sydundar/BenchVolt-PD/Firmware/USB_Power_Source/Core/Src/soft_i2c_3.c

#include <soft_i2c_3.h>

#define true 1
#define false 0

#define I2C3_GPIO_Port GPIOC

/*
#define I2C3_CLEAR_SDA HAL_GPIO_WritePin(I2C3_GPIO_Port, SDA3_Pin, GPIO_PIN_RESET)
#define I2C3_SET_SDA HAL_GPIO_WritePin(I2C3_GPIO_Port, SDA3_Pin, GPIO_PIN_SET)
#define I2C3_CLEAR_SCL HAL_GPIO_WritePin(I2C3_GPIO_Port, SCL3_Pin, GPIO_PIN_RESET)
#define I2C3_SET_SCL HAL_GPIO_WritePin(I2C3_GPIO_Port, SCL3_Pin, GPIO_PIN_SET)
*/
#define I2C3_SET_SDA        (I2C3_GPIO_Port->BSRR = (uint32_t)SDA3_Pin)
#define I2C3_CLEAR_SDA      (I2C3_GPIO_Port->BSRR = (uint32_t)SDA3_Pin << 16U)

#define I2C3_SET_SCL        (I2C3_GPIO_Port->BSRR = (uint32_t)SCL3_Pin)
#define I2C3_CLEAR_SCL      (I2C3_GPIO_Port->BSRR = (uint32_t)SCL3_Pin << 16U)


#define I2C3_DELAY delay3_us(1)

#define MCP4725_ADDR 0x60<<1
#define VHIGH_ADDRS	0x75<<1


bool set_dacVLow(uint16_t reg_data)
{
    reg_data &= 0x0FFF;
    uint8_t data[2];
    data[0] = (reg_data >> 8) & 0x0F;
    data[0] |= 0x00;

    data[1] = reg_data & 0xFF;

     return I2C3_transmit(MCP4725_ADDR, data, 2);
}




void delay3_us(uint32_t us) {
    uint32_t startTick = SysTick->VAL;
    uint32_t ticks = us * (SystemCoreClock / 1000000);
    while ((startTick - SysTick->VAL) < ticks);
}

void I2C3_init(void)
{
    I2C3_SET_SDA;
    I2C3_SET_SCL;
}

void I2C3_start_cond(void)
{
    I2C3_SET_SCL;
    I2C3_SET_SDA;
    I2C3_DELAY;
    I2C3_CLEAR_SDA;
    I2C3_DELAY;
    I2C3_CLEAR_SCL;
    I2C3_DELAY;
}

void I2C3_stop_cond(void)
{
    I2C3_CLEAR_SDA;
    I2C3_DELAY;
    I2C3_SET_SCL;
    I2C3_DELAY;
    I2C3_SET_SDA;
    I2C3_DELAY;
}

void I2C3_write_bit(uint8_t b)
{
    if (b > 0)
        I2C3_SET_SDA;
    else
        I2C3_CLEAR_SDA;

    I2C3_DELAY;
    I2C3_SET_SCL;
    I2C3_DELAY;
    I2C3_CLEAR_SCL;
}

uint8_t I2C3_read_SDA(void)
{
    if (HAL_GPIO_ReadPin(I2C3_GPIO_Port, SDA3_Pin) == GPIO_PIN_SET)
        return 1;
    else
        return 0;
    return 0;
}

// Reading a bit in I2C3:
uint8_t I2C3_read_bit(void)
{
    uint8_t b;

    I2C3_SET_SDA;
    I2C3_DELAY;
    I2C3_SET_SCL;
    I2C3_DELAY;

    b = I2C3_read_SDA();

    I2C3_CLEAR_SCL;

    return b;
}

_Bool I2C3_write_byte(uint8_t B,
                     _Bool start,
                     _Bool stop)
{
    uint8_t ack = 0;

    if (start)
        I2C3_start_cond();

    uint8_t i;
    for (i = 0; i < 8; i++)
    {
        I2C3_write_bit(B & 0x80); // write the most-significant bit
        B <<= 1;
    }

    ack = I2C3_read_bit();

    if (stop)
        I2C3_stop_cond();

    return !ack; //0-ack, 1-nack
}

// Reading a byte with I2C3:
uint8_t I2C3_read_byte(_Bool ack, _Bool stop)
{
    uint8_t B = 0;

    uint8_t i;
    for (i = 0; i < 8; i++)
    {
        B <<= 1;
        B |= I2C3_read_bit();
    }

    if (ack)
        I2C3_write_bit(0);
    else
        I2C3_write_bit(1);

    if (stop)
        I2C3_stop_cond();

    return B;
}

// Sending a byte with I2C3:
_Bool I2C3_send_byte(uint8_t address,
                    uint8_t data)
{
    //    if( I2C3_write_byte( address << 1, true, false ) )   // start, send address, write
    if (I2C3_write_byte(address, true, false)) // start, send address, write
    {
        // send data, stop
        if (I2C3_write_byte(data, false, true))
            return true;
    }

    I2C3_stop_cond(); // make sure to impose a stop if NAK'd
    return false;
}



// Sending a byte of data with I2C3:
_Bool I2C3_send_byte_data(uint8_t address,
                         uint8_t reg,
                         uint8_t data)
{
    if (I2C3_write_byte(address, true, false))
    {
        if (I2C3_write_byte(reg, false, false)) // send desired register
        {
            if (I2C3_write_byte(data, false, true))
                return true; // send data, stop
        }
    }

    I2C3_stop_cond();
    return false;
}

// Receiving a byte of data with I2C3:
uint8_t I2C3_receive_byte_data(uint8_t address,
                              uint8_t reg)
{

    if (I2C3_write_byte(address, true, false))
    {
        if (I2C3_write_byte(reg, false, false)) // send desired register
        {
            if (I2C3_write_byte((address) | 0x01, true, false)) // start again, send address, read
            {
                return I2C3_read_byte(false, true); // read data
            }
        }
    }

    I2C3_stop_cond();
    return 0; // return zero if NACKed
}




_Bool I2C3_transmit(uint8_t address, uint8_t data[], uint8_t size)
{
    if (I2C3_write_byte(address, true, false)) // first byte
    {
        for (int i = 0; i < size; i++)
        {
            if (i == size - 1)
            {
                if (I2C3_write_byte(data[i], false, true))
                    return true;
            }
            else
            {
                if (!I2C3_write_byte(data[i], false, false))
                    break; //last byte
            }
        }
    }

    I2C3_stop_cond();
    return false;
}

_Bool I2C3_receive(uint8_t address, uint8_t reg[], uint8_t *data, uint8_t reg_size, uint8_t size)
{
    if (I2C3_write_byte(address, true, false))
    {
        for (int i = 0; i < reg_size; i++)
        {
            if (!I2C3_write_byte(reg[i], false, false))
                break;
        }
        if (I2C3_write_byte(address | 0x01, true, false)) // start again, send address, read
        {
            for (int j = 0; j < size; j++)
            {
                _Bool ack = (j < size - 1);
                _Bool stop = (j == size - 1);
                *data++ = I2C3_read_byte(ack, stop);
            }
            return true;
        }
    }
    I2C3_stop_cond();
    return false;
}


//////////////////////////////////////////////////////////////////////////
//////////////////////////////////////////////////////////////////////////
//////////////////////////////////////////////////////////////////////////


void VAdjHigh_InitInternalFeedback() {
	uint8_t status1 = I2C3_receive_byte_data(VHIGH_ADDRS, REG_STATUS);
	uint8_t status2 = I2C3_receive_byte_data(VHIGH_ADDRS, REG_STATUS);

    uint8_t vfs = I2C3_receive_byte_data(VHIGH_ADDRS, REG_VOUT_FS);
    if (vfs == 0xFF) return;
    vfs &= ~(0x80 | 0x03);
    vfs |= 0x03;
    I2C3_send_byte_data(VHIGH_ADDRS, REG_VOUT_FS, vfs);
}

void VAdjHigh_EnableOutput(bool en) {
    uint8_t mode = I2C3_receive_byte_data(VHIGH_ADDRS, REG_MODE);
    if (en) mode |= 0x80;
    else mode &= ~0x80;
    I2C3_send_byte_data(VHIGH_ADDRS, REG_MODE, mode);
}

void VAdjHigh_SetVoltage(float voltage) {
    if (voltage < TPS_VOUT_MIN_V) voltage = TPS_VOUT_MIN_V;
    if (voltage > TPS_VOUT_MAX_V) voltage = TPS_VOUT_MAX_V;

    float vrefV = voltage * TPS_FB_RATIO_VAL;
    float codeF = (vrefV - TPS_VREF_OFFSET_V) / TPS_VREF_LSB_V;

    if (codeF < 0.0f) codeF = 0.0f;
    if (codeF > TPS_VREF_MAXCODE) codeF = (float)TPS_VREF_MAXCODE;

    uint16_t code = (uint16_t)(codeF + 0.5f);
    I2C3_send_byte_data(VHIGH_ADDRS, REG_REF_LSB, (uint8_t)(code & 0xFF));
    I2C3_send_byte_data(VHIGH_ADDRS, REG_REF_MSB, (uint8_t)((code >> 8) & 0x07));
}

void VAdjHigh_SetCurrentLimit(float current) {
    if (current <= 0.0f) {
        I2C3_send_byte_data(VHIGH_ADDRS, REG_IOUT_LIMIT, 0x00);
        return;
    }
    float vsenseV = current * TPS_RSENSE_OHM;
    float codeF = vsenseV / TPS_ISENSE_LSB_V;
    if (codeF > 127.0f) codeF = 127.0f;

    uint8_t code = (uint8_t)(codeF + 0.5f);
    I2C3_send_byte_data(VHIGH_ADDRS, REG_IOUT_LIMIT, (0x80 | (code & 0x7F)));
}

uint8_t VAdjHigh_GetStatus() {
    return I2C3_receive_byte_data(VHIGH_ADDRS, REG_STATUS);
}

/////////////////////
void InitVAdjHigh() { VAdjHigh_InitInternalFeedback(); }
void EnVAdjHighOutput(bool onoff) { VAdjHigh_EnableOutput(onoff); }
void SetVoltageVAdjHigh(float voltage){ VAdjHigh_SetVoltage(voltage); }
void SetVAdjHighCurrentLimit(float current) { VAdjHigh_SetCurrentLimit(current); }
