sydundar/BenchVolt-PD/Firmware/USB_Power_Source/Core/Inc/stm32_sw_i2c.h

/*
  stm32_sw_i2c.h - Library for implementing I2C in SW on any GPIO on STM32 MCU.
  Created by Mawaba Pascal Dao, Dec 2, 2020.
  Released into the public domain.
*/


#include "main.h"


void I2C_init(void);
void I2C_start_cond(void);
void I2C_stop_cond(void);
static inline void I2C_write_bit(uint8_t b) __attribute__((always_inline));
static inline uint8_t I2C_read_bit(void) __attribute__((always_inline));
uint8_t I2C_read_SDA(void);
_Bool I2C_write_byte(uint8_t B, _Bool start, _Bool stop);
uint8_t I2C_read_byte(_Bool ack, _Bool stop);
_Bool I2C_send_byte(uint8_t address, uint8_t data);
uint8_t I2C_receive_byte(uint8_t address);
_Bool I2C_send_byte_data(uint8_t address, uint8_t reg, uint8_t data);
uint8_t I2C_receive_byte_data(uint8_t address, uint8_t reg);
_Bool I2C_transmit(uint8_t address, uint8_t data[], uint8_t size);
_Bool I2C_receive(uint8_t address, uint8_t reg[], uint8_t *data, uint8_t reg_size, uint8_t size);

HAL_StatusTypeDef I2C_Write_USB_PD(uint8_t Port, uint16_t Address, uint8_t *DataW, uint16_t Length);

HAL_StatusTypeDef I2C_Read_USB_PD(uint8_t Port, uint16_t Address ,uint8_t *DataR ,uint16_t Length);
