sydundar/BenchVolt-PD/Firmware/USB_Power_Source/Core/Inc/STUSB_NVM.h

#include "main.h"

uint8_t Sector0[8] = {0x00,0x00,0xB0,0xAA,0x00,0x45,0x00,0x02};
uint8_t Sector1[8] = {0x00,0x40,0x9D,0x1C,0xF0,0x01,0x00,0xDF};
uint8_t Sector2[8] = {0x32,0x40,0x0F,0x01,0x32,0x0A,0xFC,0xF1};
uint8_t Sector3[8] = {0x00,0x19,0x54,0xAA,0x57,0x35,0x5F,0x00};
uint8_t Sector4[8] = {0x00,0x64,0x90,0x21,0x43,0x00,0x50,0xFB};
