sydundar/BenchVolt-PD/Firmware/Bootloader/Core/Src/main.c

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
/* Includes ------------------------------------------------------------------*/
#include "main.h"
#include "usb_device.h"

/* USER CODE BEGIN Includes */
#include <stdio.h>
#include <string.h>
#include "Flash.h"
#include "usbd_cdc_if.h"
#include "st7789.h"

// Flash Addresses
#define BOOTLOADER_FLASH_ADDR       0x08000000
#define PARAM_PAGE_ADDR			    0x0801F800    // Starts after 32KB Bootloader
#define MAIN_APP_FLASH_ADDR         0x08008000    // Starts after 2KB Config Page
#define VECTOR_TABLE_SIZE  0xC0U





// Protocol Commands
#define CMD_START                  0x01
#define CMD_DATA                   0x02
#define CMD_END                    0x03
#define CMD_JUMP_ONLY              0x04
#define CMD_ERASE_CRC              0x05
#define CMD_JUMP_ONLY              0x04
#define CMD_ERASE_CRC              0x05
// Protocol Responses
#define ACK                        0x06
#define NACK                       0x15


/* USER CODE END Includes */

CRC_HandleTypeDef hcrc;

SPI_HandleTypeDef hspi1;
DMA_HandleTypeDef hdma_spi1_tx;

void SystemClock_Config(void);
static void MX_GPIO_Init(void);
static void MX_DMA_Init(void);
static void MX_CRC_Init(void);
static void MX_SPI1_Init(void);
/* USER CODE BEGIN 0 */

char MBCodeBuiltDateTime[30];
uint8_t flashbuffer[128] __attribute__((aligned(4)));

uint8_t usb_rx_buffer[256];
volatile uint32_t usb_rx_len = 0;
volatile uint8_t usb_data_ready = 0;

uint32_t write_address = MAIN_APP_FLASH_ADDR;
uint32_t total_file_size = 0;
uint8_t bootloader_active = 0;

void SystemClock_Config(void);
static void MX_GPIO_Init(void);
static void MX_CRC_Init(void);
void PrintBuildDate(void);
void WriteToDevice(char* commandString);
void JumpToMainApp(void);
uint32_t calculate_crc32(uint8_t *data, uint32_t size);
void ReadFlashBuffer(void);
void WriteCRC(unsigned char *data);
uint32_t ReadCRC(void);
void WriteAppSize(uint32_t size);
uint32_t ReadAppSize(void);
void Bootloader_Protocol_Handler(void);
void Send_USB_Response(uint8_t res);

void PrintBuildDate(void)
{
    snprintf(MBCodeBuiltDateTime, 30, "%s %s", __DATE__, __TIME__);
    WriteToDevice("Code Build Date: ");
    WriteToDevice(MBCodeBuiltDateTime);
    WriteToDevice("\r\n\r\n");
}

void WriteToDevice(char* commandString)
{
    CDC_Transmit_FS((uint8_t*)commandString, strlen(commandString));
}


void JumpToMainApp(void)
{
    uint32_t appStack = *(volatile uint32_t*)MAIN_APP_FLASH_ADDR;
    uint32_t appEntry = *(volatile uint32_t*)(MAIN_APP_FLASH_ADDR + 4);

    if ((appStack < 0x20000000U) || (appStack > 0x20004000U))
        return;

    __disable_irq();

    SysTick->CTRL = 0;
    SysTick->LOAD = 0;
    SysTick->VAL  = 0;

    USB->CNTR = USB_CNTR_FRES;
    USB->CNTR = 0;
    USB->BCDR &= ~USB_BCDR_DPPU;
    __HAL_RCC_USB_CLK_DISABLE();

    for (uint32_t i = 0; i < 8; i++)
    {
        NVIC->ICER[i] = 0xFFFFFFFF;
        NVIC->ICPR[i] = 0xFFFFFFFF;
    }

    for (uint32_t i = 0; i < VECTOR_TABLE_SIZE / 4; i++)
    {
        ((volatile uint32_t*)0x20000000U)[i] =
            ((volatile uint32_t*)MAIN_APP_FLASH_ADDR)[i];
    }

    __HAL_RCC_SYSCFG_CLK_ENABLE();

    SYSCFG->CFGR1 &= ~SYSCFG_CFGR1_MEM_MODE;
    SYSCFG->CFGR1 |= SYSCFG_CFGR1_MEM_MODE_0 | SYSCFG_CFGR1_MEM_MODE_1;

    __DSB();
    __ISB();

    __set_MSP(appStack);

    ((void (*)(void))appEntry)();

    while (1);
}


uint32_t calculate_crc32(uint8_t *data, uint32_t size)
{
    uint32_t crc = 0xFFFFFFFF;
    for (uint32_t i = 0; i < size; i++)
    {
        crc = crc ^ (uint32_t)data[i];
        for (uint32_t j = 0; j < 8; j++)
        {
            if (crc & 0x80000000) crc = (crc << 1) ^ 0x04C11DB7;
            else crc <<= 1;
        }
    }
    return crc;
}

void ReadFlashBuffer(void)
{
    ReadFlash((uint32_t*)PARAM_PAGE_ADDR, (uint32_t*)flashbuffer, 32);
}

void WriteCRC(unsigned char *data)
{
    ReadFlashBuffer();
    flashbuffer[16] = data[0]; flashbuffer[17] = data[1];
    flashbuffer[18] = data[2]; flashbuffer[19] = data[3];
    WriteFlash(PARAM_PAGE_ADDR, (uint32_t*)flashbuffer, sizeof(flashbuffer)/sizeof(uint32_t));
    HAL_Delay(10);
}

void WriteBootParams(uint32_t crc, uint32_t size)
{
    FLASH_EraseInitTypeDef EraseInitStruct;
    uint32_t PageError = 0;

    HAL_FLASH_Unlock();

    // Sadece parametre sayfasını sil (Uygulamaya asla dokunmaz)
    EraseInitStruct.TypeErase = FLASH_TYPEERASE_PAGES;
    EraseInitStruct.PageAddress = PARAM_PAGE_ADDR;
    EraseInitStruct.NbPages = 1;
    HAL_FLASHEx_Erase(&EraseInitStruct, &PageError);

    // CRC ve Boyut bilgilerini mühürle
    HAL_FLASH_Program(FLASH_TYPEPROGRAM_WORD, PARAM_PAGE_ADDR, crc);
    HAL_FLASH_Program(FLASH_TYPEPROGRAM_WORD, PARAM_PAGE_ADDR + 4, size);

    HAL_FLASH_Lock();
}


uint32_t ReadCRC(void)
{
    return *(volatile uint32_t*)PARAM_PAGE_ADDR;
}

uint32_t ReadAppSize(void)
{
    return *(volatile uint32_t*)(PARAM_PAGE_ADDR + 4);
}

void WriteAppSize(uint32_t size)
{
    ReadFlashBuffer();
    flashbuffer[20] = (uint8_t)(size & 0xFF);
    flashbuffer[21] = (uint8_t)((size >> 8) & 0xFF);
    flashbuffer[22] = (uint8_t)((size >> 16) & 0xFF);
    flashbuffer[23] = (uint8_t)((size >> 24) & 0xFF);
    WriteFlash(PARAM_PAGE_ADDR, (uint32_t*)flashbuffer, sizeof(flashbuffer)/sizeof(uint32_t));
    HAL_Delay(10);
}



void Send_USB_Response(uint8_t res)
{
    uint32_t start_tick = HAL_GetTick();
    while (CDC_Transmit_FS(&res, 1) == USBD_BUSY)
    {
        if ((HAL_GetTick() - start_tick) > 100) break;
        HAL_Delay(1);
    }
}

void Bootloader_Protocol_Handler(void)
{
    if (!usb_data_ready) return;
    uint8_t cmd = usb_rx_buffer[0];

    if (cmd == CMD_START)
        {
            total_file_size = usb_rx_buffer[1] | (usb_rx_buffer[2] << 8) | (usb_rx_buffer[3] << 16) | (usb_rx_buffer[4] << 24);
            write_address = MAIN_APP_FLASH_ADDR;
            bootloader_active = 1;

            //Bootloader_ShowProgress(0, total_file_size);
            WriteBootParams(0xFFFFFFFF, 0xFFFFFFFF);  // Delete existing CRC

            if (Flash_EraseAppArea(MAIN_APP_FLASH_ADDR, total_file_size) == 0) Send_USB_Response(ACK);
            else Send_USB_Response(NACK);
        }

    else if (cmd == CMD_DATA && bootloader_active)
        {
            uint16_t len = usb_rx_buffer[1] | (usb_rx_buffer[2] << 8);
            uint8_t *payload = &usb_rx_buffer[3];

            // DİKKAT: Veriyi 4'ün katına (Word Alignment) yuvarlıyoruz!
            uint32_t word_count = (len + 3) / 4;
            uint32_t aligned_buffer[64]; // Maksimum paket boyutunu kaldıracak havuz

            // 1. Buffer'ı 0xFF ile doldur (Boş kalan byte'lar Flash'ta 0xFF olarak kalmalıdır)
            memset(aligned_buffer, 0xFF, sizeof(aligned_buffer));

            // 2. Gelen 8-bitlik raw veriyi güvenli 32-bitlik havuza kopyala
            memcpy(aligned_buffer, payload, len);

            // 3. Özel Flash.c fonksiyonumuzu çağırarak veriyi donanıma kazı
            if (Flash_WriteWordsNoErase(write_address, aligned_buffer, word_count) == 0)
            {
                write_address += (word_count * 4); // Adresi başarılı yazılan byte kadar ileri sar
                uint32_t writtenBytes = write_address - MAIN_APP_FLASH_ADDR;
                //Bootloader_ShowProgress(writtenBytes, total_file_size);
                Send_USB_Response(ACK);
            }
            else
            {
                Send_USB_Response(NACK); // Yazma hatası oluştuysa Python'a bildir
            }
        }
    else if (cmd == CMD_END && bootloader_active)
        {
            uint32_t received_crc = usb_rx_buffer[1] | (usb_rx_buffer[2] << 8) | (usb_rx_buffer[3] << 16) | (usb_rx_buffer[4] << 24);
            uint32_t calculated_flash_crc = calculate_crc32((uint8_t*)MAIN_APP_FLASH_ADDR, total_file_size);

            if (calculated_flash_crc == received_crc)
            {
                // Python'dan gelen ile hesaplanan eşleşti! Güvenle parametreyi mühürle ve zıpla!
                WriteBootParams(calculated_flash_crc, total_file_size);
                Send_USB_Response(ACK);
                HAL_Delay(200);
                JumpToMainApp();
            }
            else
            {
            uint8_t error_packet[5] = {NACK};
            error_packet[1] = (uint8_t)(calculated_flash_crc & 0xFF);
            error_packet[2] = (uint8_t)((calculated_flash_crc >> 8) & 0xFF);
            error_packet[3] = (uint8_t)((calculated_flash_crc >> 16) & 0xFF);
            error_packet[4] = (uint8_t)((calculated_flash_crc >> 24) & 0xFF);
            CDC_Transmit_FS(error_packet, 5);
        }
        bootloader_active = 0;
    }
    usb_data_ready = 0;
}

void Bootloader_ShowProgress(uint32_t writtenBytes, uint32_t totalBytes)
{
    char text[20];

    if (totalBytes == 0)
        return;

    uint32_t percent = (writtenBytes * 100U) / totalBytes;

    if (percent > 100)
        percent = 100;

    snprintf(text, sizeof(text), "%lu%%", percent);

    // Ortaya yakın bölgeyi temizle
    ST7789_DrawFilledRectangle(70, 90, 180, 140, BLACK);

    // Başlık
    ST7789_WriteString(55, 70, "Uploading", Font_11x18, WHITE, BLACK);

    // Yüzde yazısı
    ST7789_WriteString(105, 100, text, Font_16x26, GREEN, BLACK);

    // Basit progress bar çerçevesi
    ST7789_DrawRectangle(40, 135, 280, 155, WHITE);

    // İç dolum
    uint16_t barWidth = (uint16_t)((236U * percent) / 100U);
    ST7789_DrawFilledRectangle(42, 137, 42 + barWidth, 153, GREEN);
}
/* USER CODE END 0 */

/**
  * @brief  The application entry point.
  * @retval int
  */
int main(void)
{

  /* MCU Configuration--------------------------------------------------------*/

  /* Reset of all peripherals, Initializes the Flash interface and the Systick. */
  HAL_Init();

  /* Configure the system clock */
  SystemClock_Config();

  /* Initialize all configured peripherals */
  MX_GPIO_Init();
  MX_DMA_Init();
  MX_USB_DEVICE_Init();
  MX_CRC_Init();
  MX_SPI1_Init();
  /* USER CODE BEGIN 2 */
  __HAL_RCC_USB_CLK_ENABLE();
  USB->BCDR |= USB_BCDR_DPPU;


  HAL_Delay(100);
  PrintBuildDate();

  ST7789_Init();

  ST7789_WriteString(0, 0, "BOOTLOADER v1.0", Font_11x18, WHITE, BLUE);
  HAL_Delay(100);
  /* USER CODE END 2 */

  /* Infinite loop */
  /* USER CODE BEGIN WHILE */
  while (1)
  {
    /* USER CODE END WHILE */

    /* USER CODE BEGIN 3 */


	    // ====================================================================
	    // 1. ADIM: OTOMATİK ATLAMA GÜVENLİK KONTROLÜ (GÜÇ AÇILIŞI)
	    // ====================================================================
	    uint32_t expected_crc = ReadCRC();
	    uint32_t saved_app_size = ReadAppSize();

	    // Hafızada geçerli bir CRC ve mantıklı bir uygulama boyutu var mı? (Örn: max 96KB)
	    if (expected_crc != 0xFFFFFFFF && saved_app_size > 0 && saved_app_size <= (96 * 1024))
	    {
	        // Flash'taki uygulamanın gerçek CRC'sini hesapla
	        uint32_t current_flash_crc = calculate_crc32((uint8_t*)MAIN_APP_FLASH_ADDR, saved_app_size);

	        if (current_flash_crc == expected_crc)
	        {
	            // EĞER HER ŞEY DOĞRUYSA: Hiç bekleme yapmadan DOĞRUDAN ana uygulamaya zıpla!
	            JumpToMainApp();
	        }
	    }

	    // ====================================================================
	    // 2. ADIM: EĞER GEÇERLİ UYGULAMA YOKSA VEYA UPLOADER BAĞLIYSA
	    // ====================================================================
	    WriteToDevice("No Valid App or CRC Mismatch. Staying in Bootloader Mode...\r\n");

	    // Ana Döngü: Gelen tüm uploader komutlarını ve ham test butonlarını dinler
	    while (1)
	    {
	        // Bootloader modunda çakılı kaldığını göstermek için LED'leri flaşör yap
	        static uint32_t last_wait_hb = 0;
	        if ((HAL_GetTick() - last_wait_hb) > 150)
	        {
	            HAL_GPIO_TogglePin(GPIOB, LED_BLUE_Pin);
	            HAL_GPIO_TogglePin(GPIOB, LED_RED_Pin);
	            last_wait_hb = HAL_GetTick();
	        }

	        if (usb_data_ready)
	        {
	            uint8_t cmd = usb_rx_buffer[0];

	            if (cmd == CMD_JUMP_ONLY)
	            {
	                WriteToDevice("Ham Emir: Uygulamaya atlanıyor...\r\n");
	                Send_USB_Response(ACK);
	                HAL_Delay(100);
	                JumpToMainApp();
	            }
	            else if (cmd == CMD_ERASE_CRC)
	            {
	                WriteToDevice("Ham Emir: CRC Alanı temizleniyor...\r\n");
	                uint8_t invalid_crc[4] = {0xFF, 0xFF, 0xFF, 0xFF};
	                WriteCRC(invalid_crc);
	                Send_USB_Response(ACK);
	            }
	            else
	            {
	                // Protokolün can damarı: CMD_START, CMD_DATA ve CMD_END akışını işletir
	                // Dosya yüklemesi bittiğinde kendisi otomatik olarak WriteCRC ve JumpToMainApp çağıracak!
	                Bootloader_Protocol_Handler();
	            }

	            usb_data_ready = 0; // Bayrağı indir
	        }
	    }
  }
  /* USER CODE END 3 */
}

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
